AndreasNielsen4000/Group-6-Telekommunikation/Project/keypad/lcd_display.h

#ifndef lcd_display_h
#define lcd_display_h

#include <LiquidCrystal_I2C.h>
#include "Arduino.h"


extern LiquidCrystal_I2C lcd;

class lcd_display
{
private:

public:
    lcd_display();
    void init();
    void enterPasswordLCD(char user[]);
    void updatePasswordLCD();
    void wrongPasswordLCD();
    void accessGrantedLCD(int userIndex);
    void adminMenuLCD(int userIndex);
    void presentRFIDLCD();
};


#endif
